jie326513988/T12Touch-screen-welding-machines/3D打印件/壳-改.png

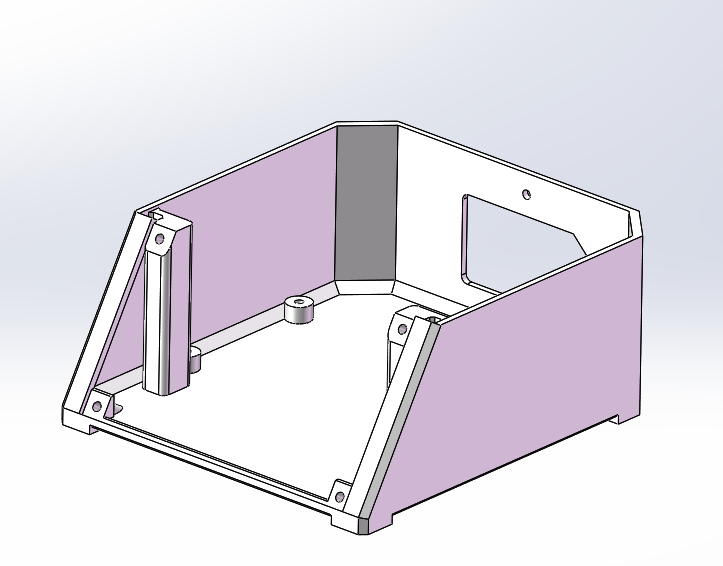
3D打印件/壳-改.png
