jie326513988/T12Touch-screen-welding-machines/compressed image/02.jpg

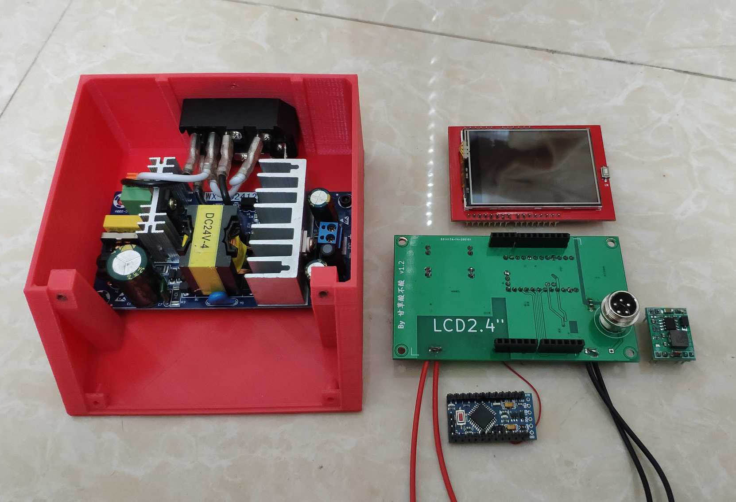
compressed image/02.jpg
