jie326513988/T12Touch-screen-welding-machines/compressed image/03.jpg

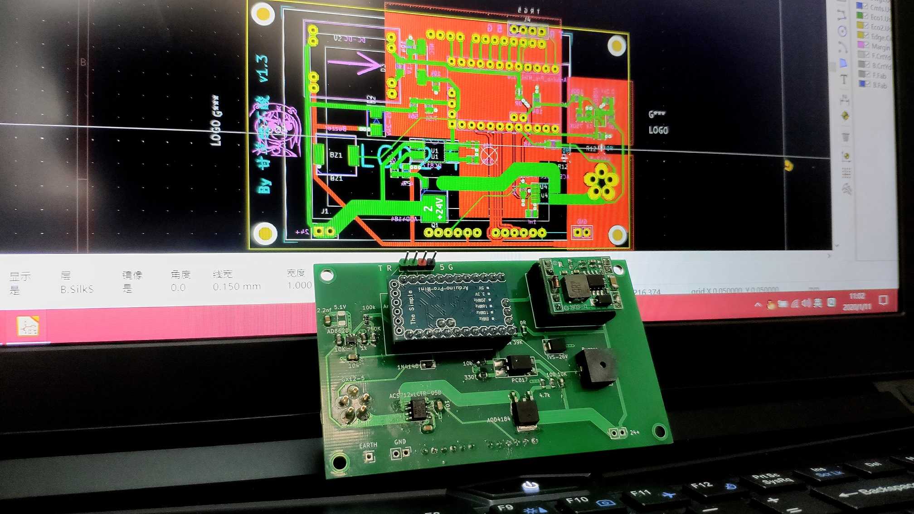
compressed image/03.jpg
