jie326513988/T12Touch-screen-welding-machines/compressed image/04.jpg

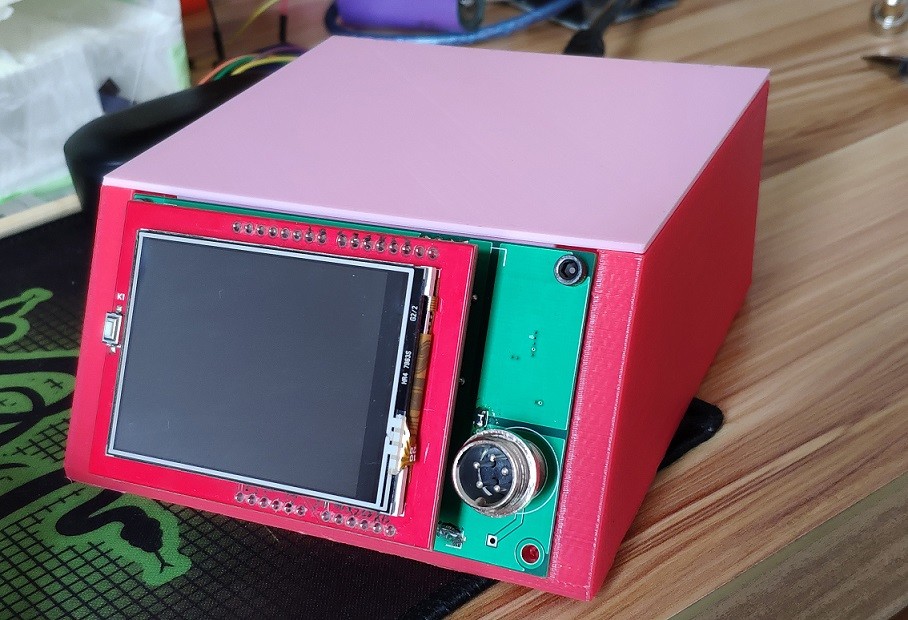
compressed image/04.jpg
