jie326513988/T12Touch-screen-welding-machines/PCB-V2.4/V2.4-PCB背面.png

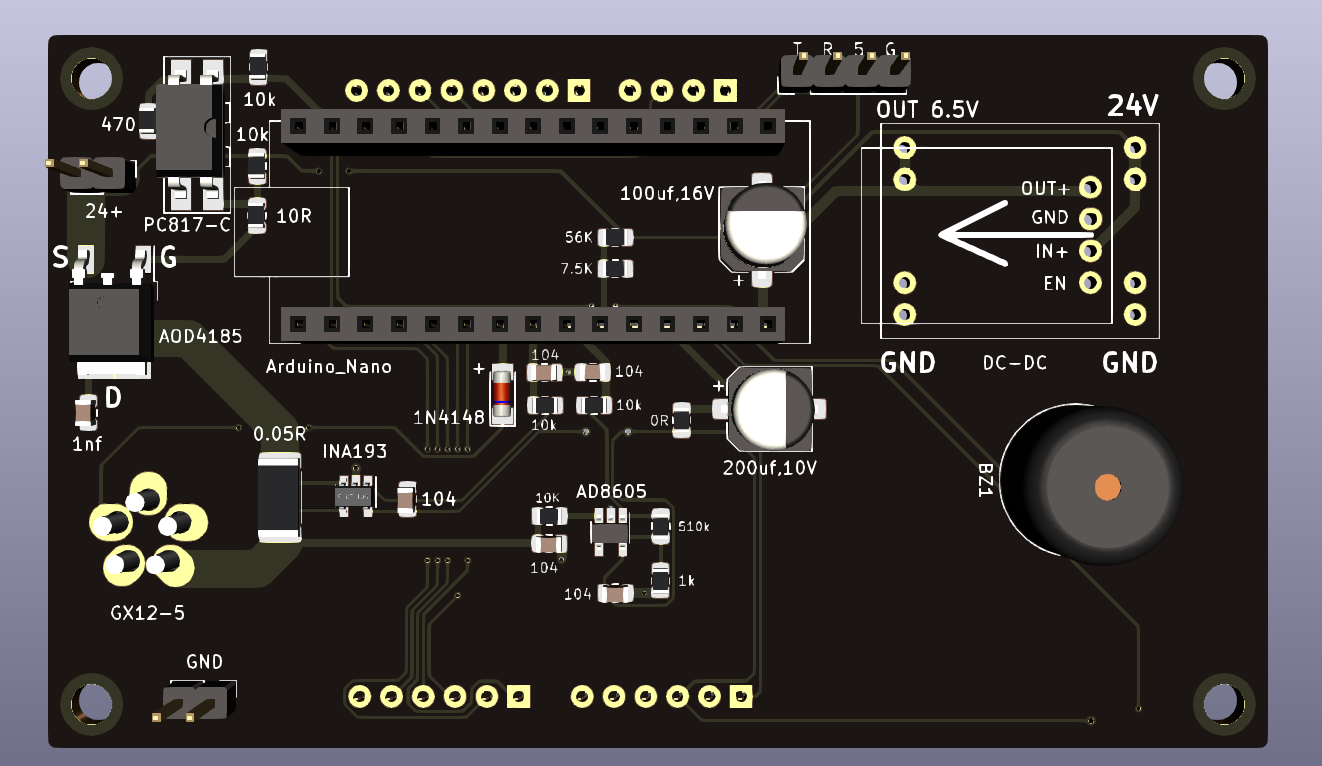
PCB-V2.4/V2.4-PCB背面.png
